monty124/USBPowerBlock/PCB_Trace.png

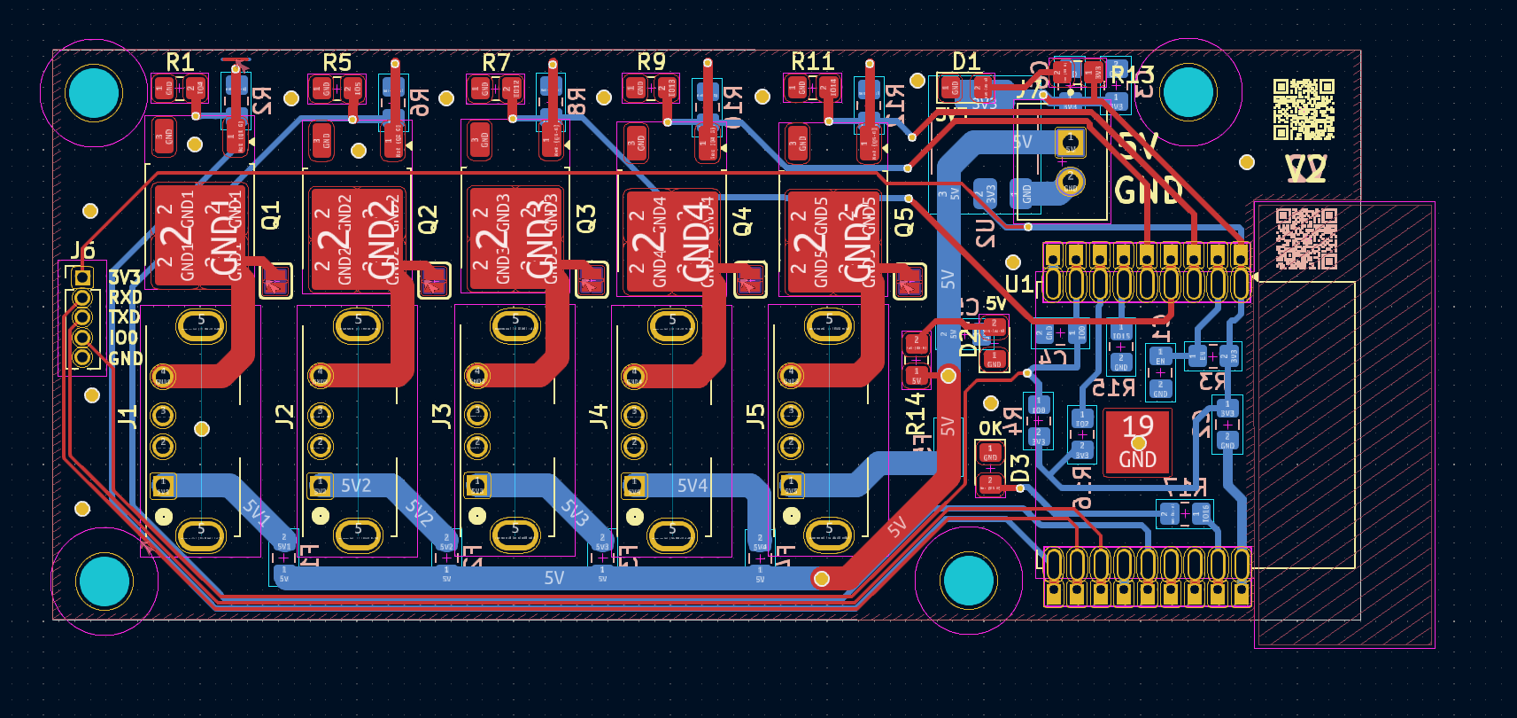
PCB_Trace.png
