monty124/USBPowerBlock/Assembly/20251019_123500.jpg

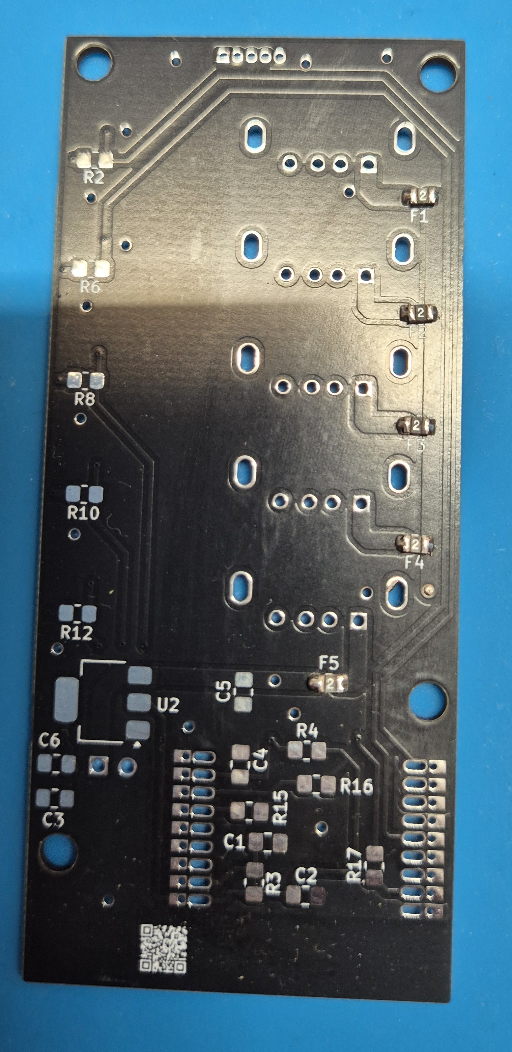
Assembly/20251019_123500.jpg
