monty124/USBPowerBlock/Assembly/20251019_123642.jpg

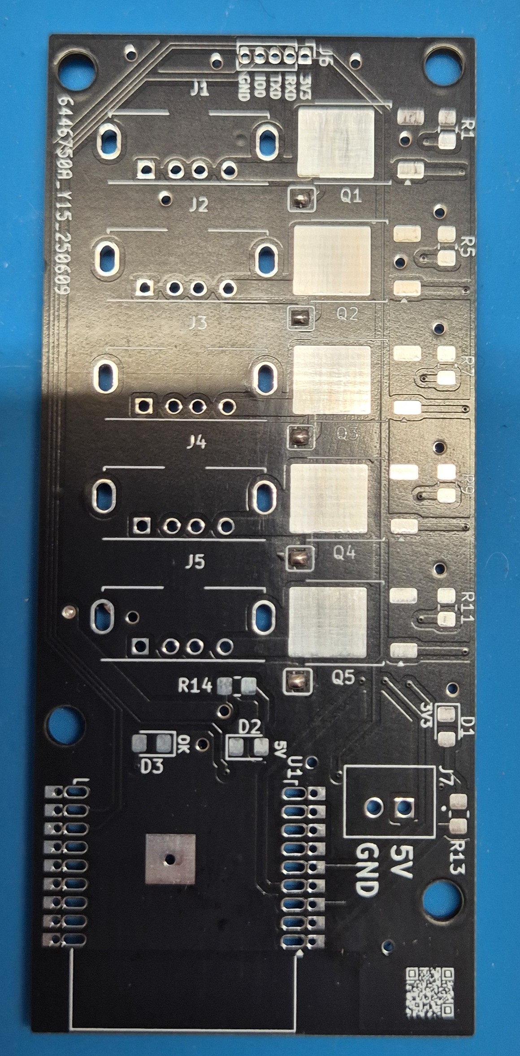
Assembly/20251019_123642.jpg
