monty124/USBPowerBlock/Assembly/20251019_124030.jpg

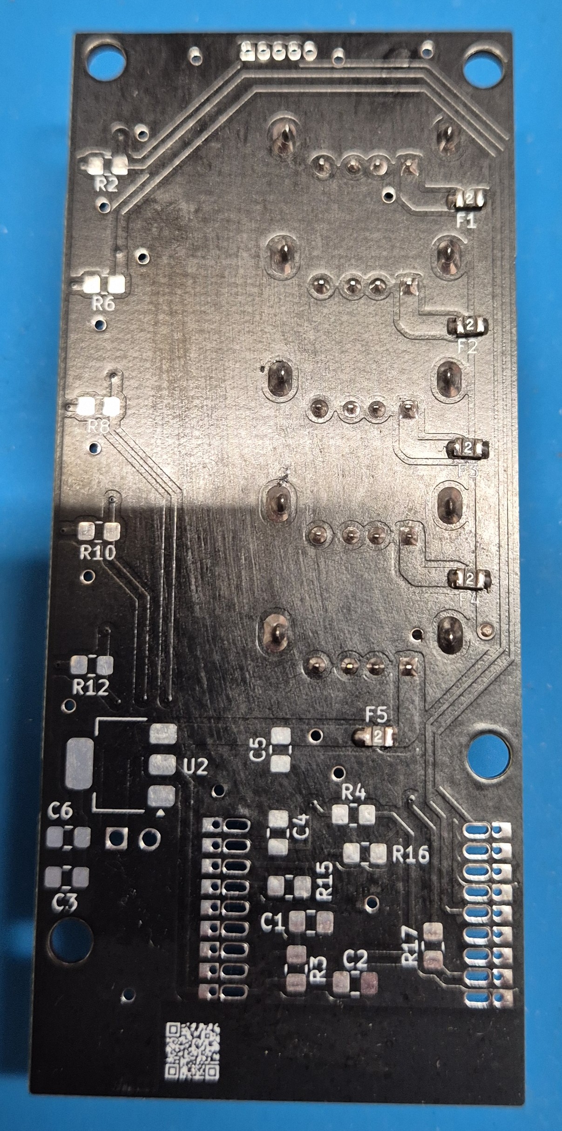
Assembly/20251019_124030.jpg
