monty124/USBPowerBlock/Assembly/20251019_124120.jpg

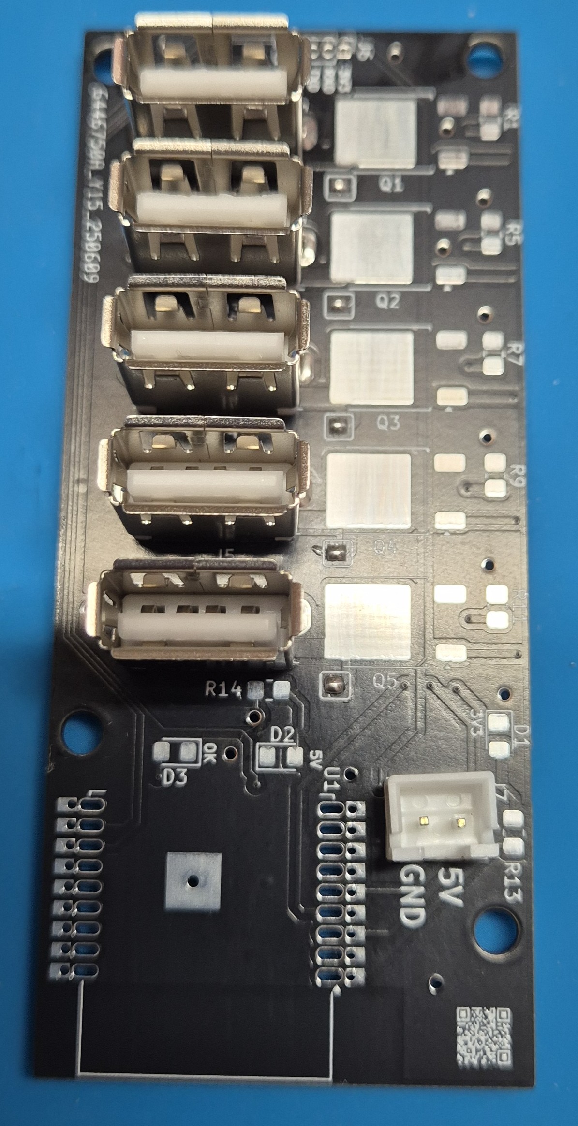
Assembly/20251019_124120.jpg
