monty124/USBPowerBlock/Assembly/20251019_124127.jpg

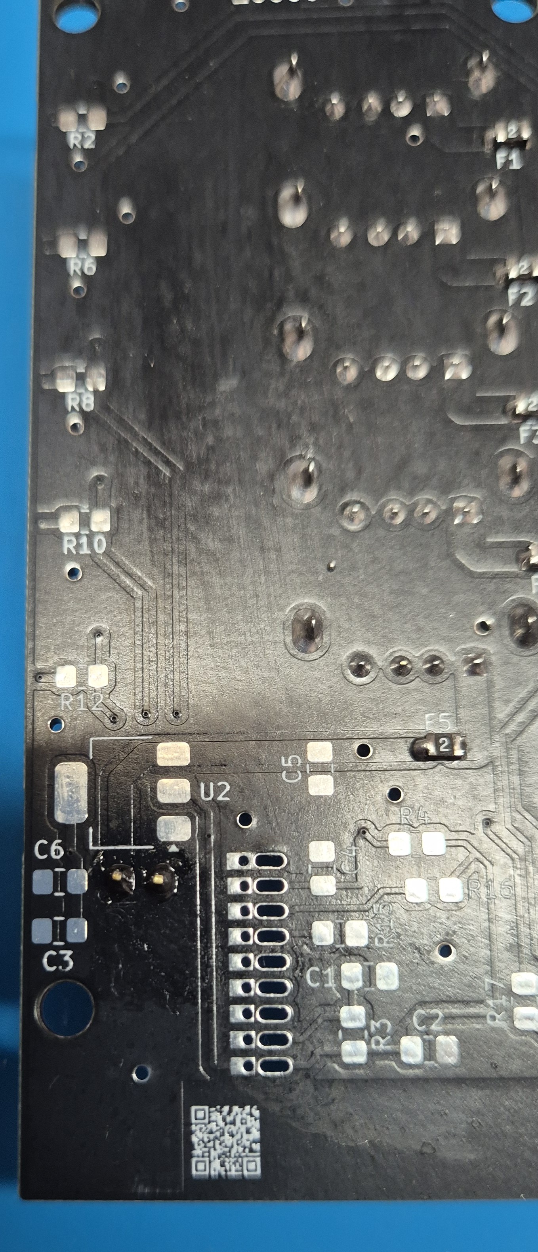
Assembly/20251019_124127.jpg
