monty124/USBPowerBlock/Assembly/20251019_125226.jpg

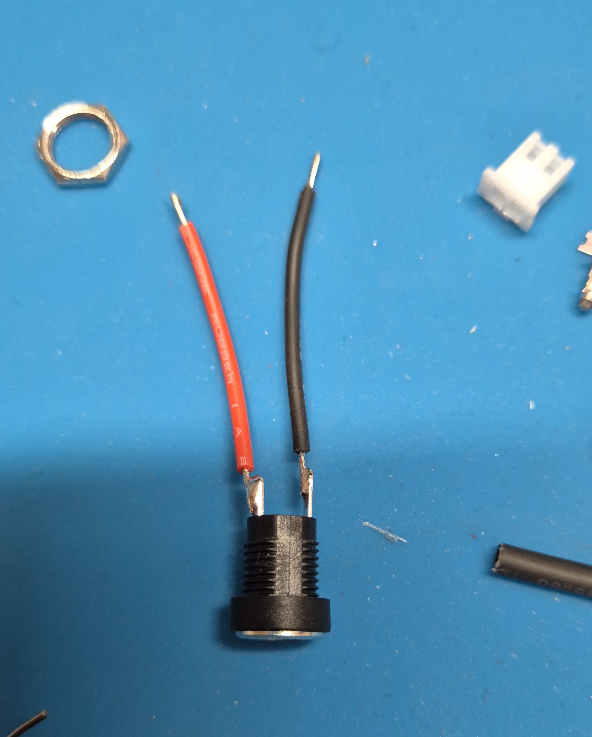
Assembly/20251019_125226.jpg
