monty124/USBPowerBlock/Assembly/20251019_130804.jpg

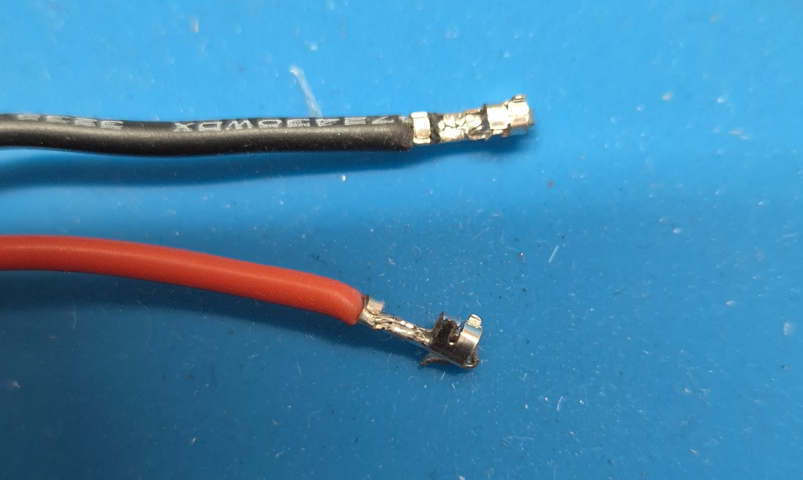
Assembly/20251019_130804.jpg
